keeweelol/Hikers-Companion/Lora Source/dimensions/README.md

# Shell

| Board | Shell |
| --- | --- |
| T-Beam-Supreme | [Shell](./T-Beam-Suppeme.7z) |
| T-Beam-V1.1/V1.2 | [Shell](./T-Beam-V1X.7z) |
| T3-V2.1-1.6 | [Shell](./T3-V2.1-1.6.7z) |
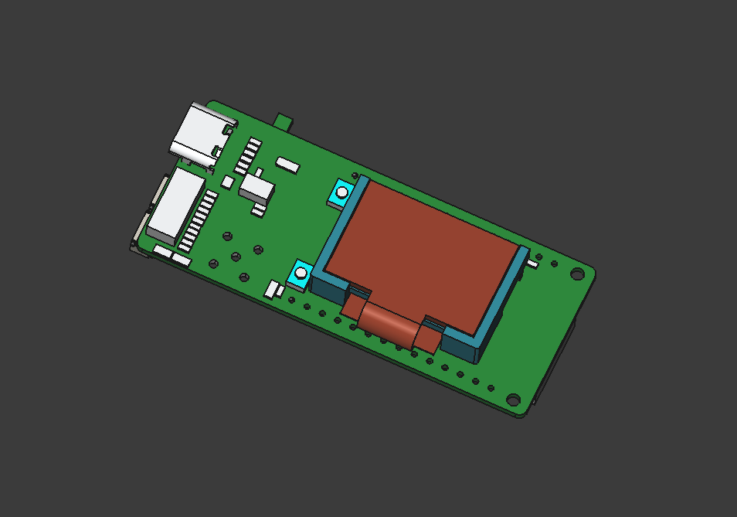
[picture p22: Lora Source/dimensions/images/T3S3-OLED.png]
| T3-S3 OLED |  |
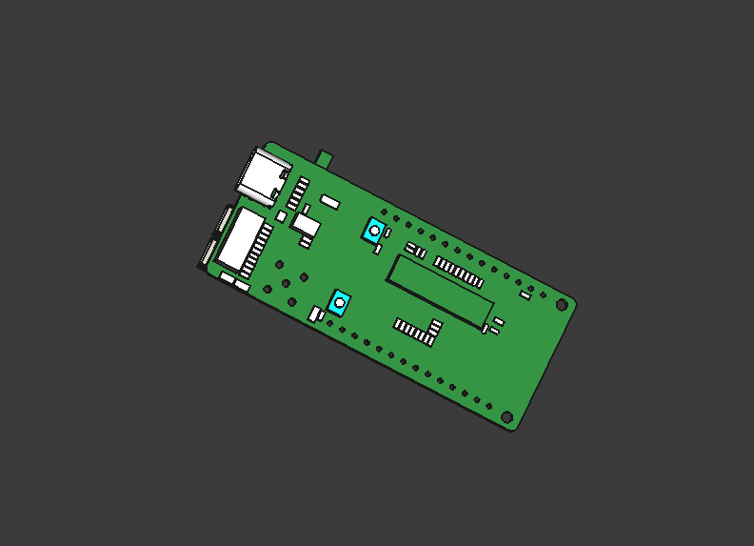
[picture p23: Lora Source/dimensions/images/T3S3.png]
| T3-S3 |  |
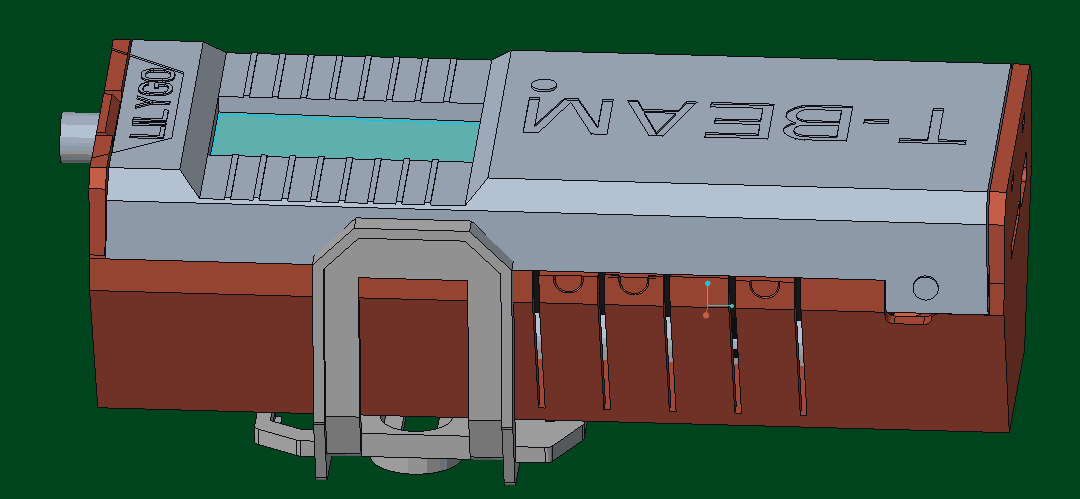
[picture p24: Lora Source/dimensions/images/T-Beam-Supreme-Shell.png]
Shell
| T-Beam-Supreme-Shell.7z |  |
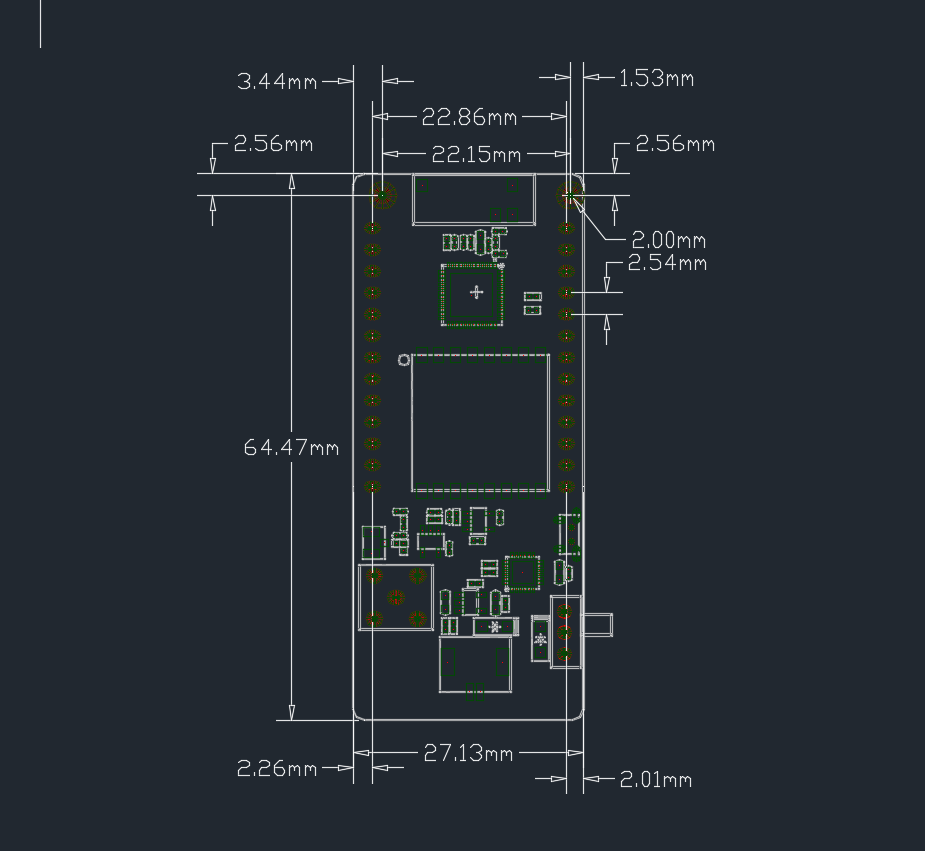
[picture p25: Lora Source/dimensions/images/T3-V1.6-DXF.png]
| T3-V1.6.2 |  |
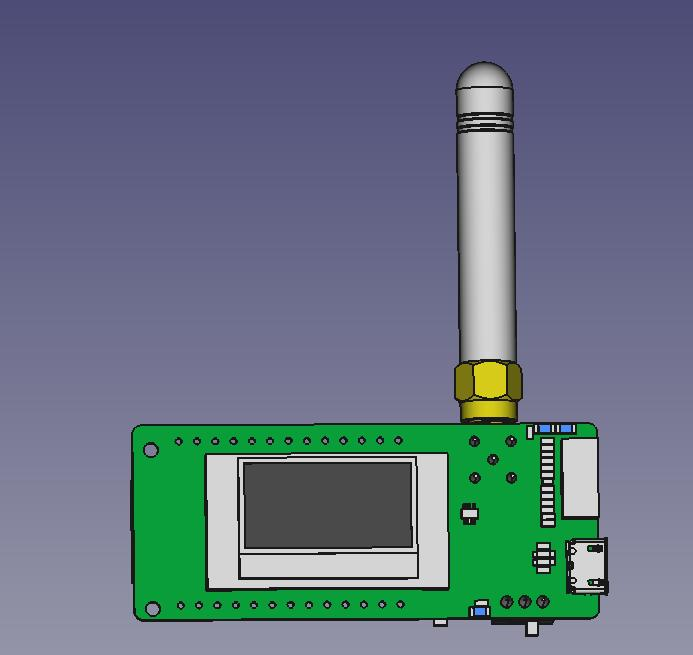
[picture p26: Lora Source/dimensions/images/T3-V1.6-PCB.jpg]
| T3_V1.6_PCB_3D.7z |  |
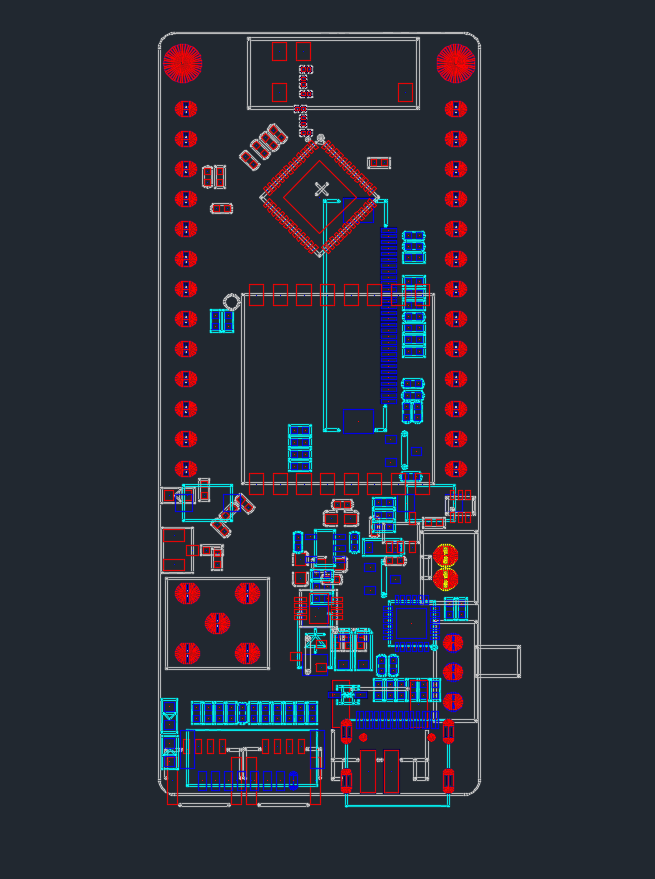
[picture p27: Lora Source/dimensions/images/T3 TCXO.png]
| TT3_V3.0_TCXO |  |
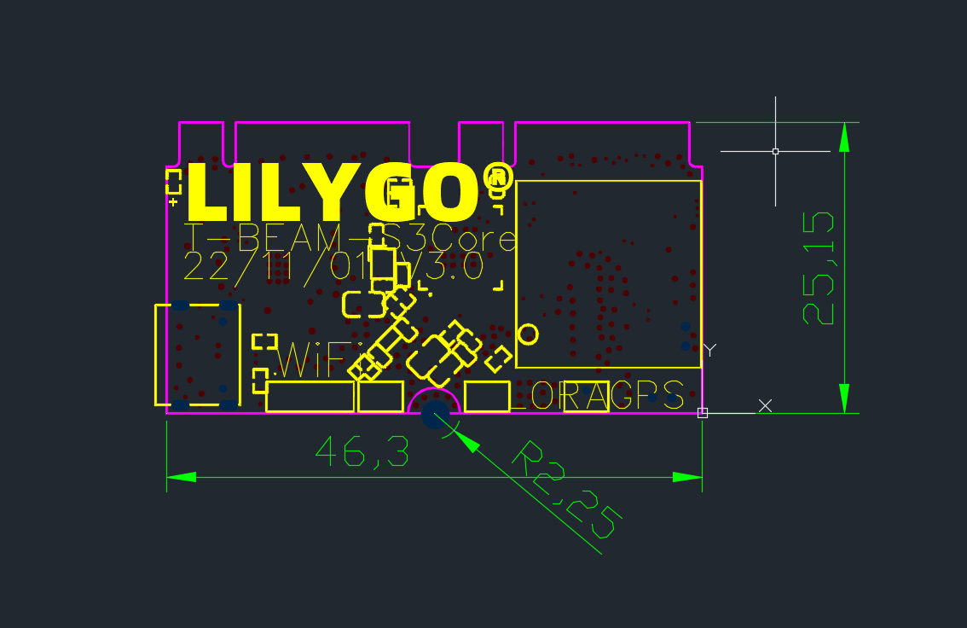
[picture p28: Lora Source/dimensions/images/T-Beam-S3.png]
| T-Beam-S3-Core |  |
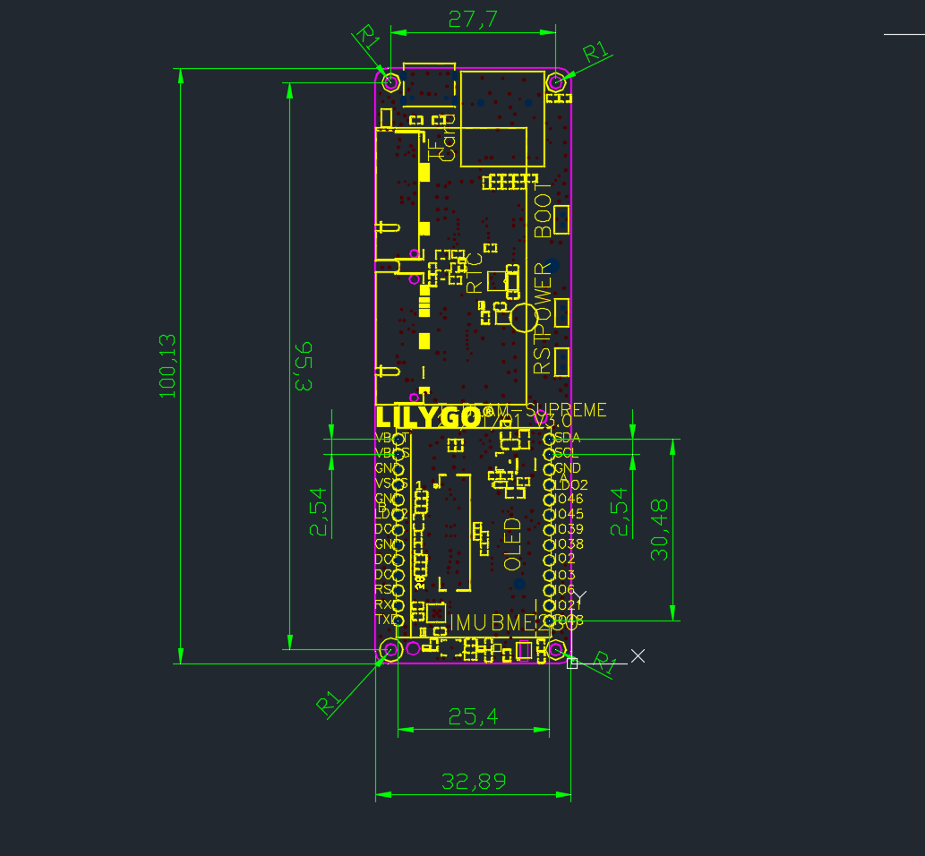
[picture p29: Lora Source/dimensions/images/T-Beam-Supreme.png]
| T-Beam-Supreme |  |
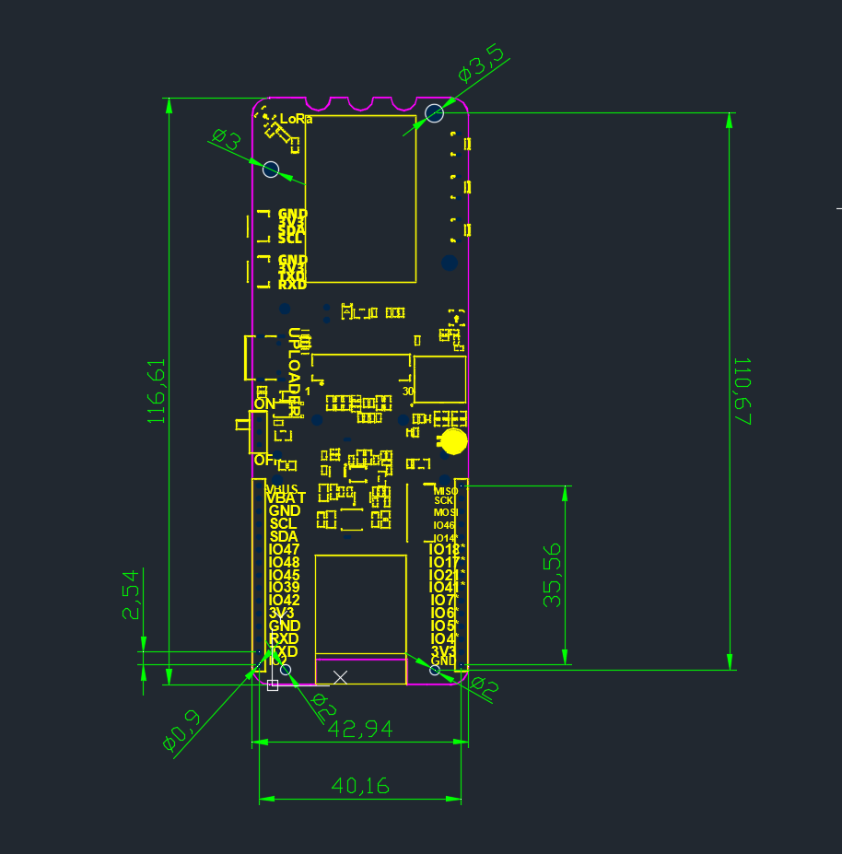
[picture p30: Lora Source/dimensions/images/t-beam-1w-dwg.png]
| T-Beam-1W |  |
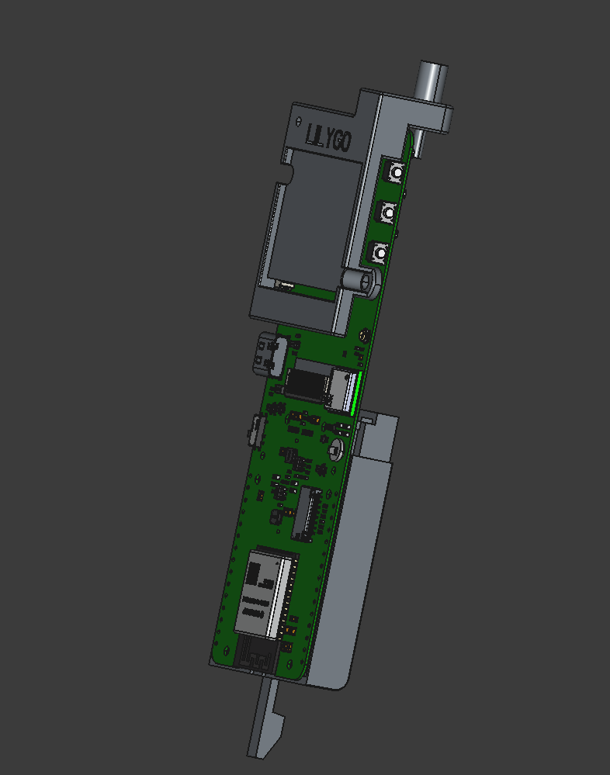
[picture p31: Lora Source/dimensions/images/t-beam-1w.png]
| T-Beam-1W |  |
