keeweelol/Hikers-Companion/Lora Source/assets/image/GPS_EN.jpg

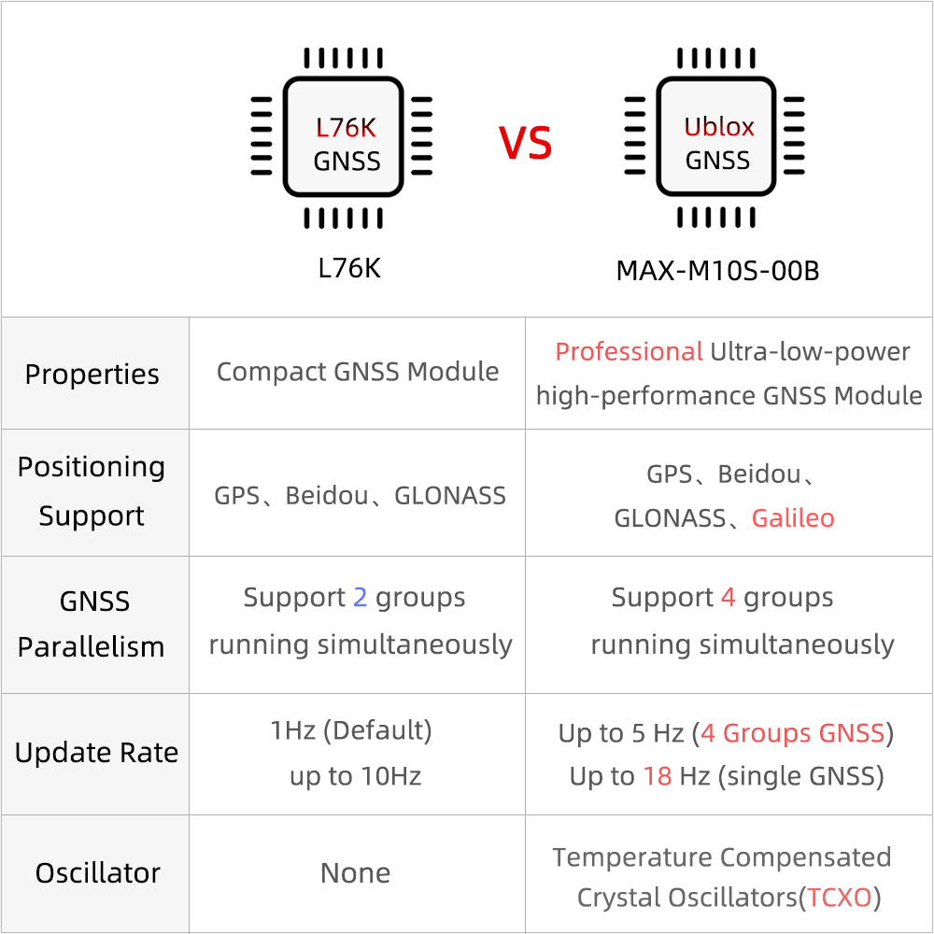
Lora Source/assets/image/GPS_EN.jpg
