keeweelol/Hikers-Companion/Lora Source/assets/image/lora32_v1.3_pinmap.jpg

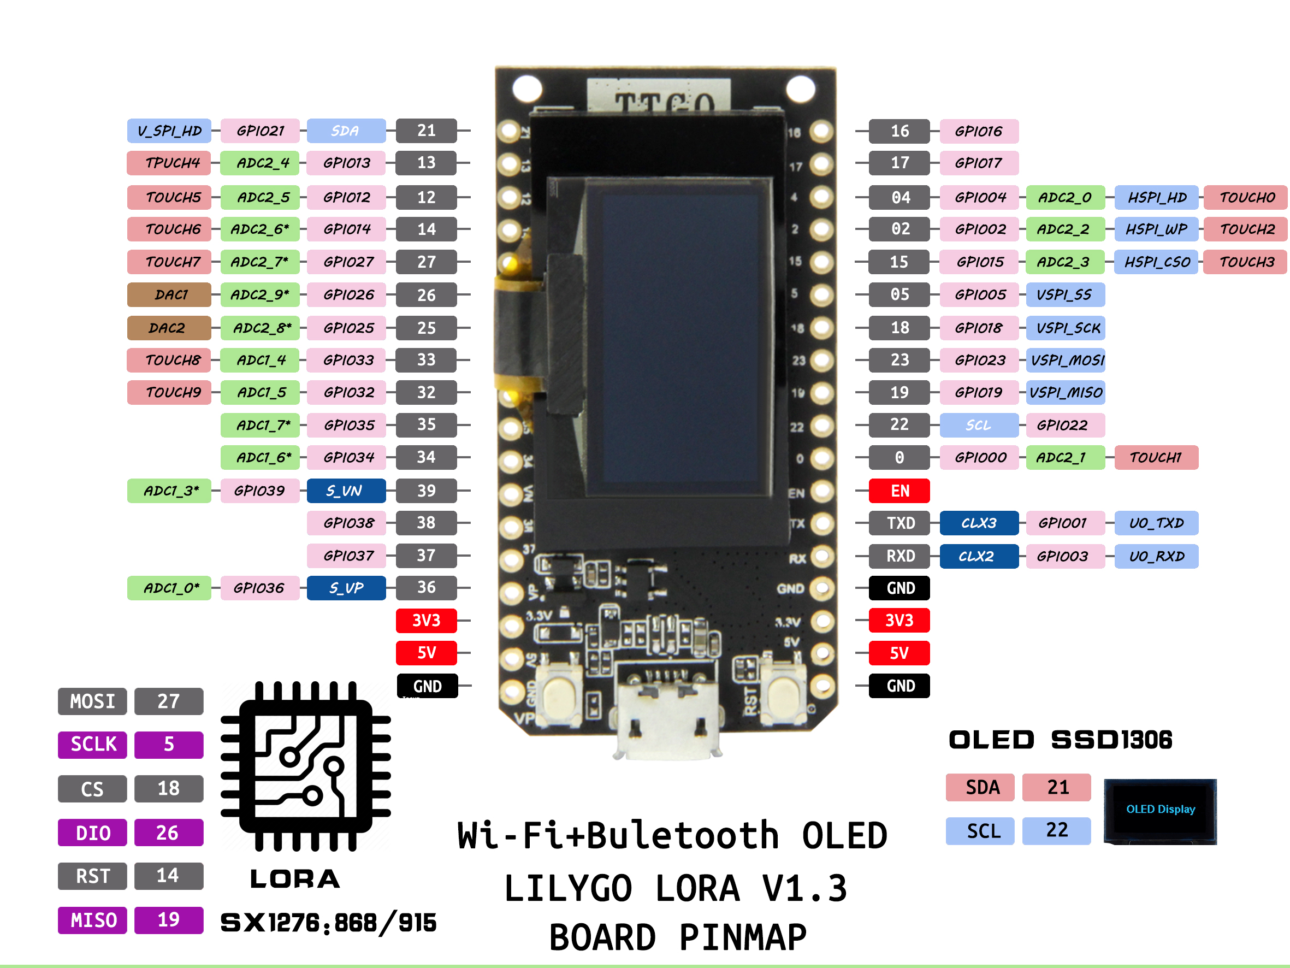
Lora Source/assets/image/lora32_v1.3_pinmap.jpg
