keeweelol/Hikers-Companion/Lora Source/assets/image/lora32_v1.8_pinmap.jpg

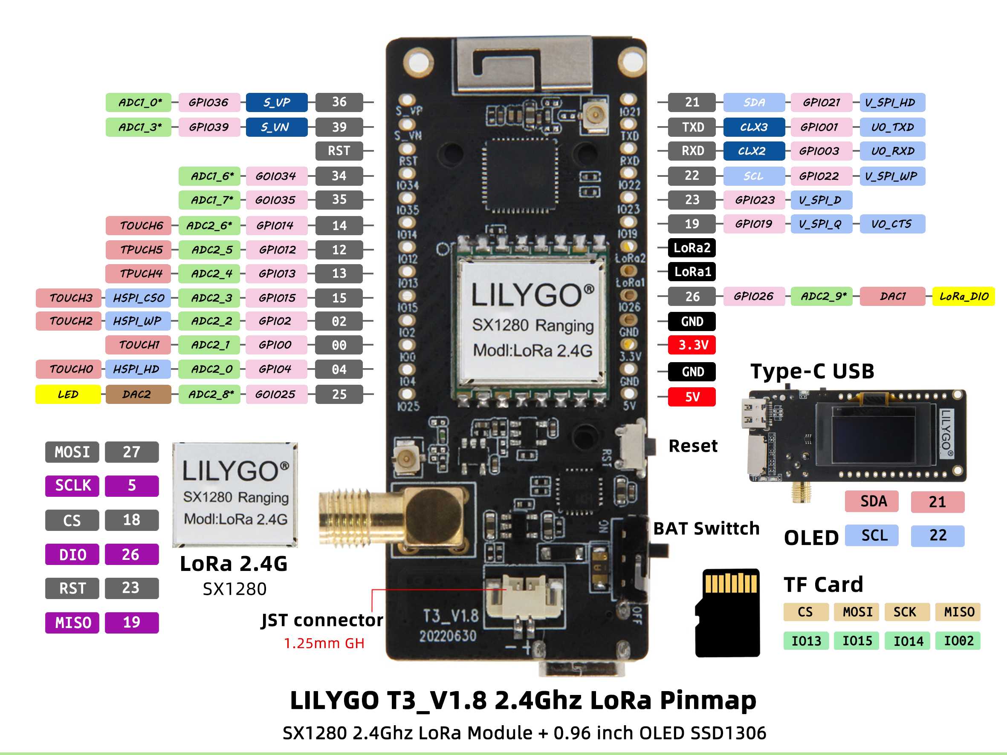
Lora Source/assets/image/lora32_v1.8_pinmap.jpg
