keeweelol/Hikers-Companion/Lora Source/assets/image/lora32_v2.0_pinmap.jpg

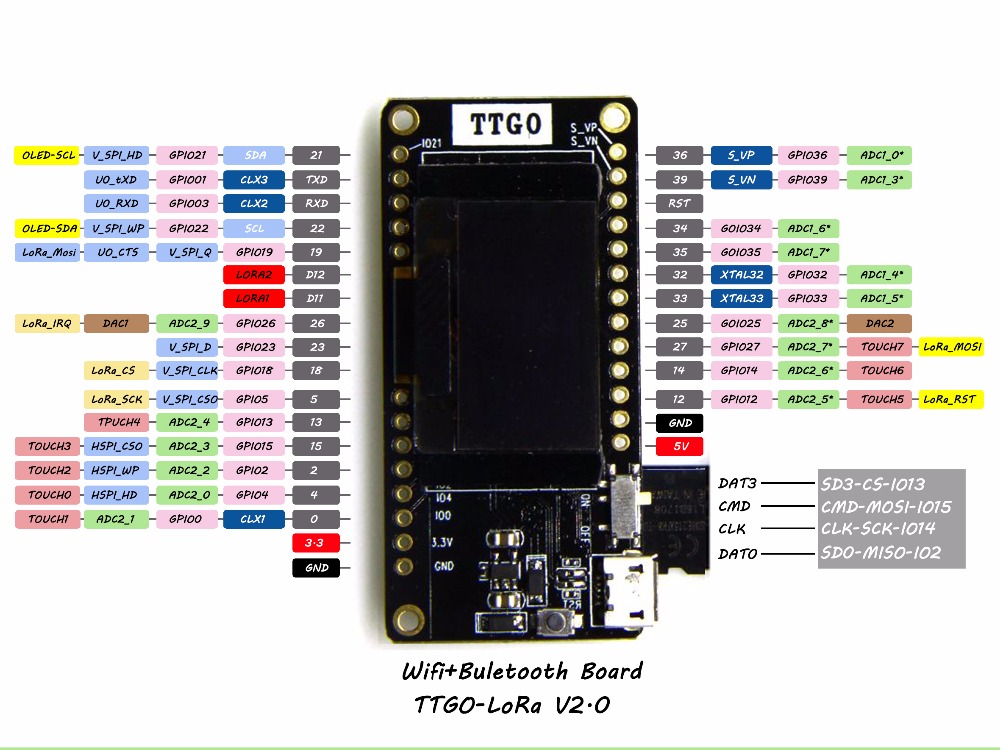
Lora Source/assets/image/lora32_v2.0_pinmap.jpg
