keeweelol/Hikers-Companion/Lora Source/assets/image/T-BEAM-S3-Supreme.jpg

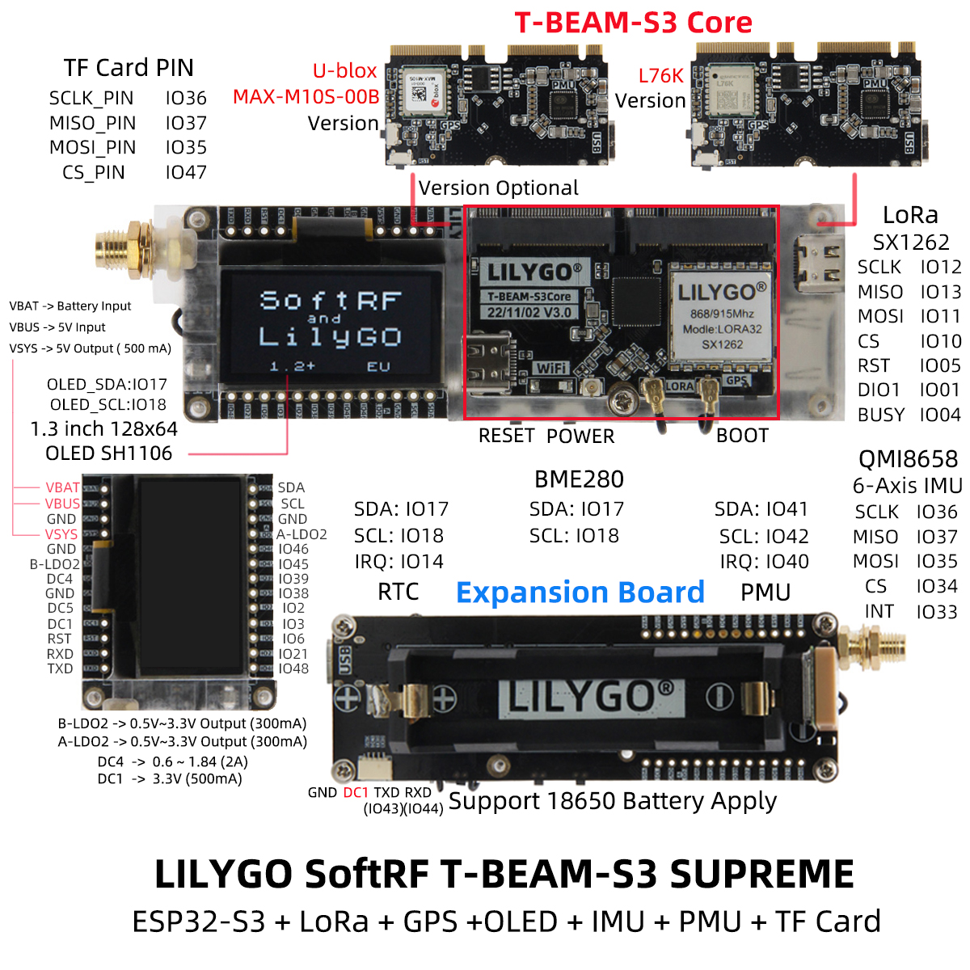
Lora Source/assets/image/T-BEAM-S3-Supreme.jpg
