keeweelol/Hikers-Companion/Lora Source/assets/image/t-beam_v1.1_pinmap.jpg

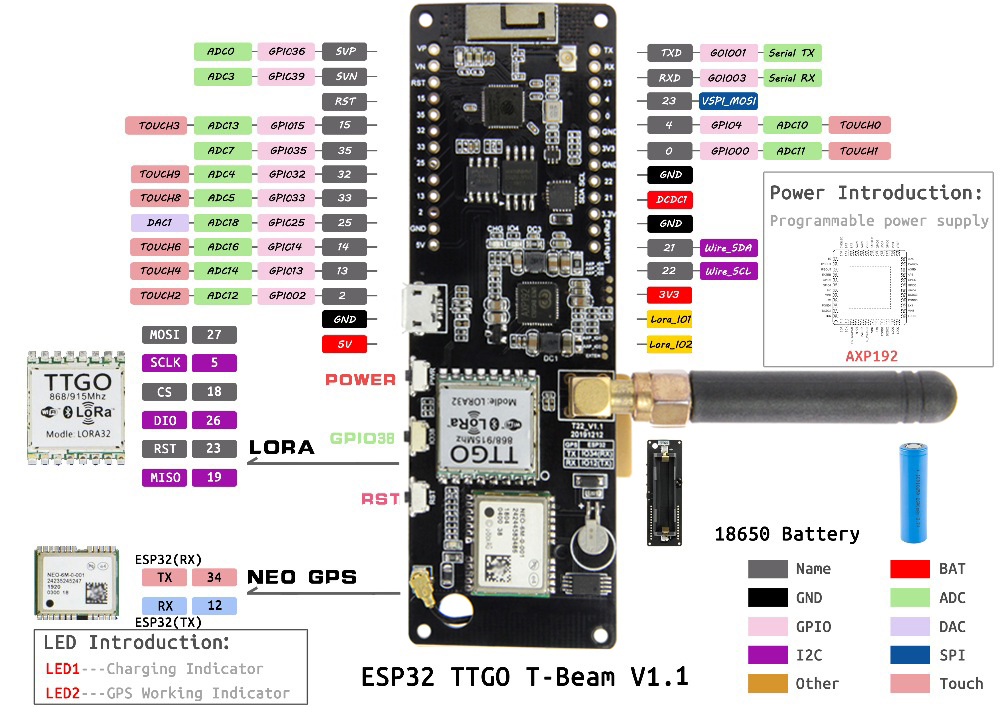
Lora Source/assets/image/t-beam_v1.1_pinmap.jpg
