keeweelol/Hikers-Companion/Lora Source/assets/image/t-motion_v1.0_pinmap.jpg

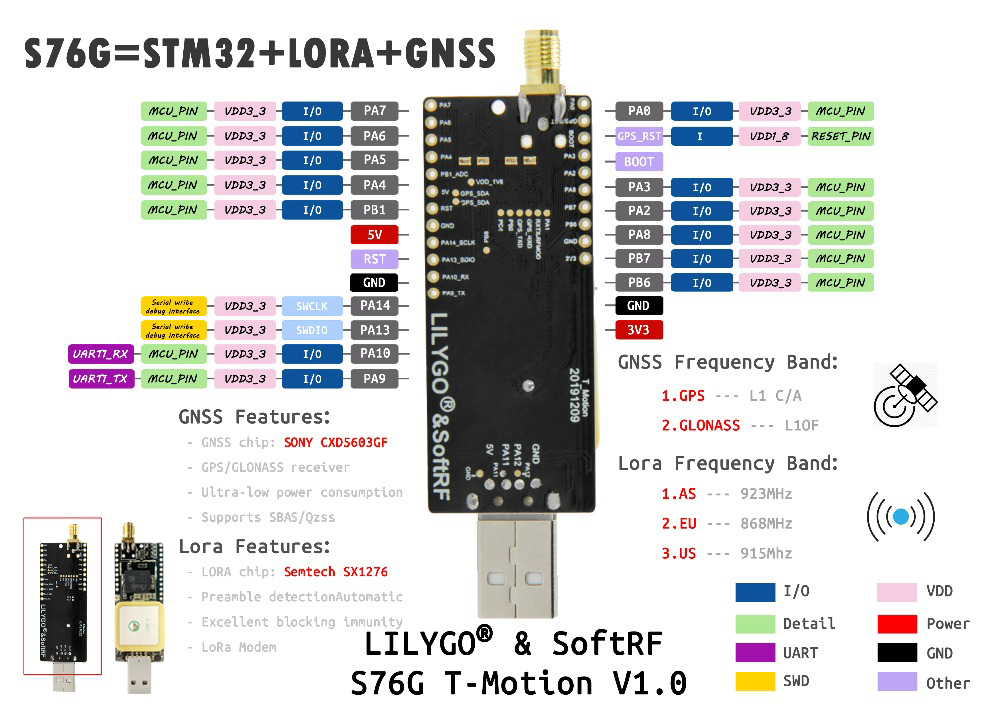
Lora Source/assets/image/t-motion_v1.0_pinmap.jpg
