keeweelol/Hikers-Companion/Lora Source/examples/T3S3Factory/images/T3_S3_V1.3_DeepSleepCurrent.jpg

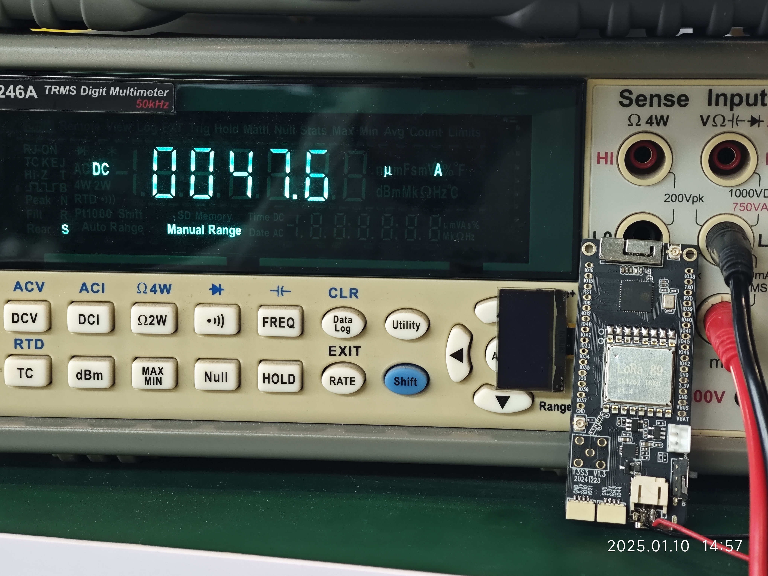
Lora Source/examples/T3S3Factory/images/T3_S3_V1.3_DeepSleepCurrent.jpg
