keeweelol/Hikers-Companion/Lora Source/examples/TBeamFactory/images/TIMER_WAKEUP_ADD_GPIO_WAKEUP_ext1_ext0_SLEEP_CUR.jpg

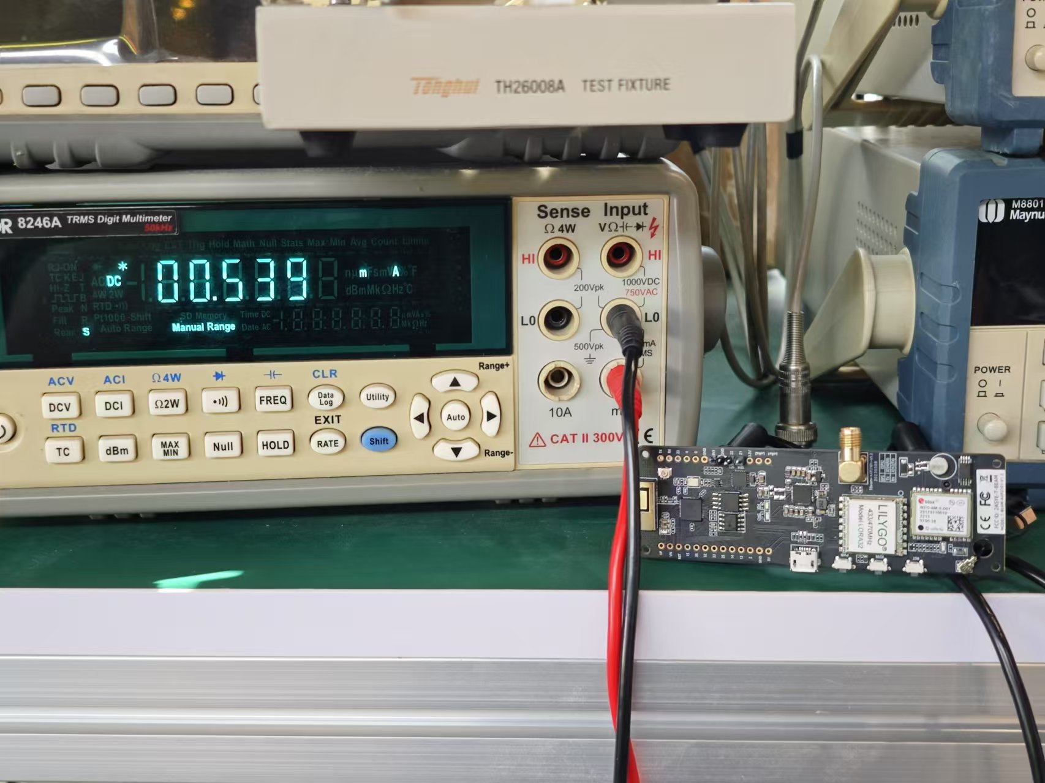
Lora Source/examples/TBeamFactory/images/TIMER_WAKEUP_ADD_GPIO_WAKEUP_ext1_ext0_SLEEP_CUR.jpg
