keeweelol/Hikers-Companion/Lora Source/examples/TBeamFactory/images/TIMER_WAKEUP_ADD_GPIO_WAKEUP_SLEEP_CUR_Disp.jpg

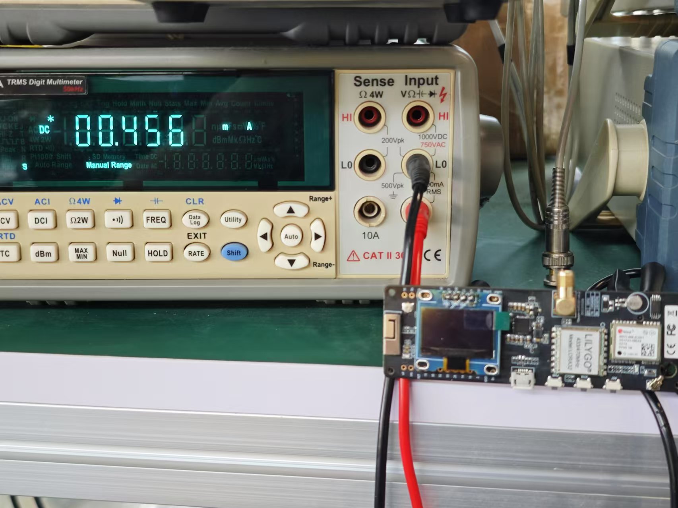
Lora Source/examples/TBeamFactory/images/TIMER_WAKEUP_ADD_GPIO_WAKEUP_SLEEP_CUR_Disp.jpg
