keeweelol/Hikers-Companion/Lora Source/firmware/images/u-center2.gif

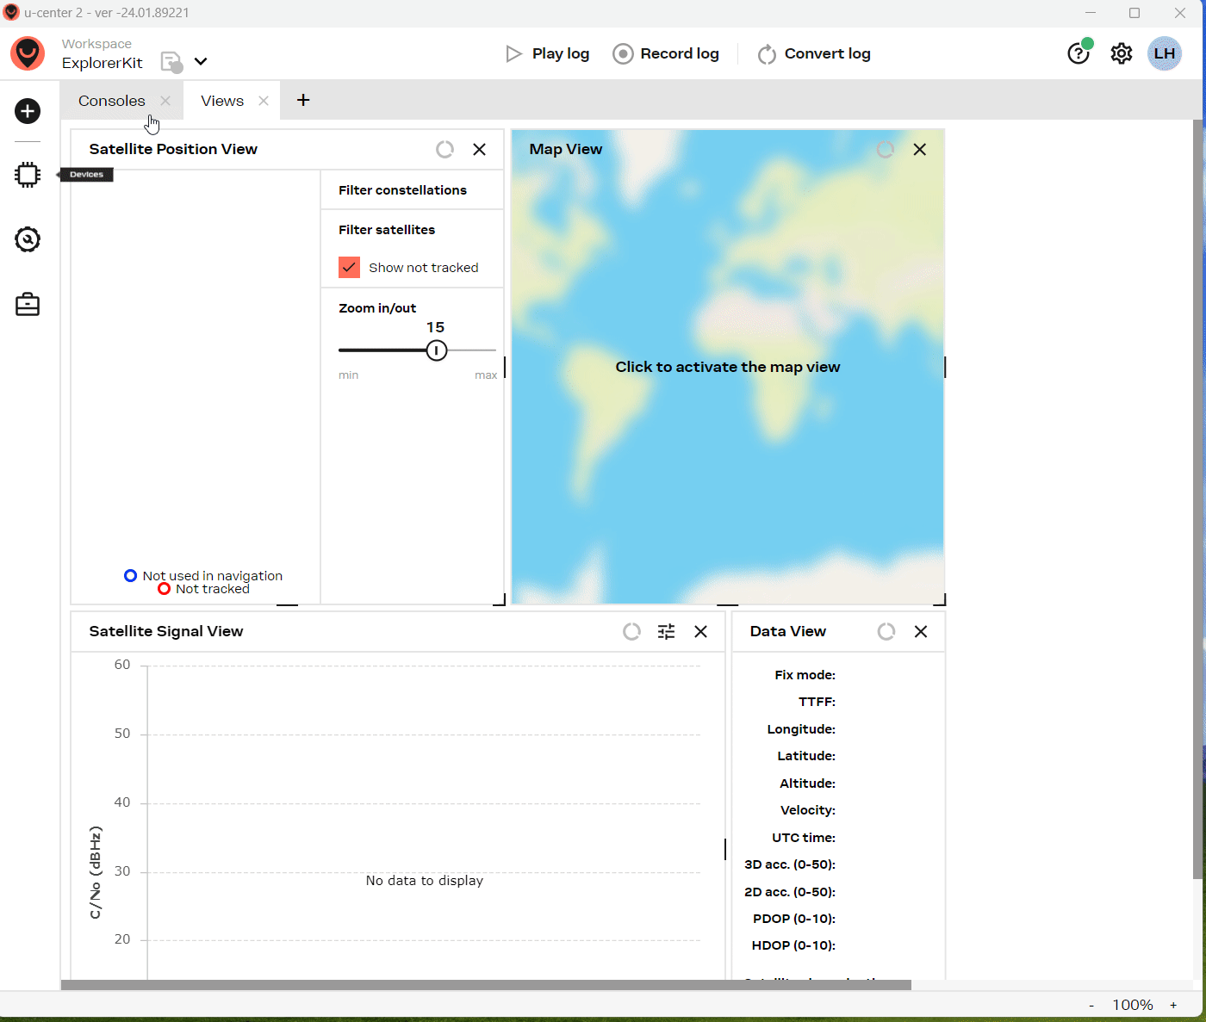
Lora Source/firmware/images/u-center2.gif
