keeweelol/Hikers-Companion/Lora Source/firmware/hardware_test/lT3_C6_V1.0_850/SETTING.jpg

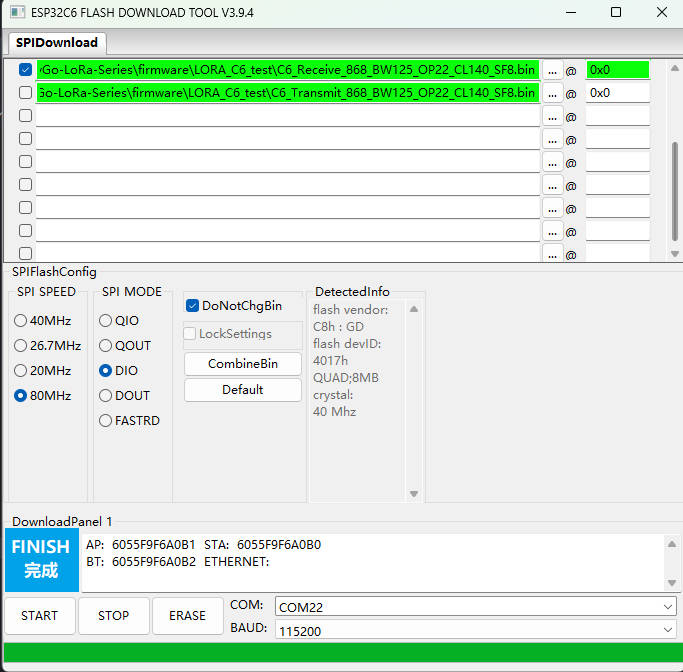
Lora Source/firmware/hardware_test/lT3_C6_V1.0_850/SETTING.jpg
