keeweelol/Hikers-Companion/Lora Source/examples/OLED/SH1106FontUsage/SH1106FontUsage.ino

/*

  FontUsage.ino

  How to overwrite previous text with a new text.
  How to avoid the buffer clear command.

  Universal 8bit Graphics Library (https://github.com/olikraus/disp/)

  Copyright (c) 2016, olikraus@gmail.com
  All rights reserved.

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
  THIS SOFTWARE IS PROVIDED BY THE COPYRIGHT HOLDERS AND
  CONTRIBUTORS "AS IS" AND ANY EXPRESS OR IMPLIED WARRANTIES,
  INCLUDING, BUT NOT LIMITED TO, THE IMPLIED WARRANTIES OF
  MERCHANTABILITY AND FITNESS FOR A PARTICULAR PURPOSE ARE
  DISCLAIMED. IN NO EVENT SHALL THE COPYRIGHT HOLDER OR
  CONTRIBUTORS BE LIABLE FOR ANY DIRECT, INDIRECT, INCIDENTAL,
  SPECIAL, EXEMPLARY, OR CONSEQUENTIAL DAMAGES (INCLUDING, BUT
  NOT LIMITED TO, PROCUREMENT OF SUBSTITUTE GOODS OR SERVICES;
  LOSS OF USE, DATA, OR PROFITS; OR BUSINESS INTERRUPTION) HOWEVER
  CAUSED AND ON ANY THEORY OF LIABILITY, WHETHER IN CONTRACT,
  STRICT LIABILITY, OR TORT (INCLUDING NEGLIGENCE OR OTHERWISE)
  ARISING IN ANY WAY OUT OF THE USE OF THIS SOFTWARE, EVEN IF
  ADVISED OF THE POSSIBILITY OF SUCH DAMAGE.


  Usually, a sequence like this is used:
  disp->clearBuffer();                   // clear the internal memory
  disp->setFont(u8g2_font_ncenB08_tr);   // choose a suitable font
  disp->setCursor(0,20)              // set write position
  disp->print("Hello World!");           // write something to the internal memory
  disp->sendBuffer();                    // transfer internal memory to the display

  In order to speed up the display content rendering for any modified text,
  we could drop the clearBuffer command and just overwrite the previous string:

  disp->setFont(u8g2_font_ncenB08_tr);   // choose a suitable font
  disp->setCursor(0,20)              // set write position
  disp->print("hello there");            // write something to the internal memory
  disp->sendBuffer();                    // transfer internal memory to the display

  This will only work if:
  - Background is drawn
  - All gylphs have the same height
  Additionally some extra spaces are required of the new text is shorter than the
  previous one.

  To draw the background: use font mode 0
  To ensure that all glyphs have the same height, use h or m fonts.

  disp->setFontMode(0);              // write solid glyphs
  disp->setFont(u8g2_font_ncenB08_hr);   // choose a suitable h font
  disp->setCursor(0,20)              // set write position
  disp->print("hello there  ");          // use extra spaces here
  disp->sendBuffer();                    // transfer internal memory to the display


*/

#include <Arduino.h>
#include "LoRaBoards.h"


#define INFO_SCREEN_DELAY 3000

/*
  Linear Congruential Generator (LCG)
  z = (a*z + c) % m;
  m = 256 (8 Bit)

  for period:
  a-1: dividable by 2
  a-1: multiple of 4
  c: not dividable by 2

  c = 17
  a-1 = 64 --> a = 65
*/
uint8_t z = 127;    // start value
uint32_t lcg_rnd(void)
{
    z = (uint8_t)((uint16_t)65 * (uint16_t)z + (uint16_t)17);
    return (uint32_t)z;
}

void setup(void)
{
    setupBoards();
    if (!disp) {
        Serial.println("No find SH1106 display!Please check whether the connection is normal");
        while (1);
    }
}

void draw(int is_blank)
{
    int i, j;
    int n;
    char s[4];

    for ( j = 0; j < 20; j++ ) {
        // random number
        n = lcg_rnd();

        // random string
        for ( i = 0; i < 3; i++ ) {
            s[i] = lcg_rnd() >> 3;
            if ( s[i] < 16 )
                s[i] += 'a';
            else
                s[i] += 'A';
        }
        s[3] = '\0';

        // print number
        disp->setCursor(0, 15);
        disp->print("Number: ");
        if ( is_blank )
            disp->print("       ");
        disp->setCursor(70, 15);
        disp->print(n);


        // print string
        disp->setCursor(0, 30);
        disp->print("Text: ");
        disp->setCursor(70, 30);
        disp->print(s);
        if ( is_blank )
            disp->print("        ");

        // make the result visible
        disp->sendBuffer();

        // delay, so that the user can see the result
        delay(200);
    }
}

void draw_m1_t()
{
    disp->clearBuffer();

    disp->setFontMode(1);
    disp->setFont(u8g2_font_cu12_tr);

    disp->setCursor(0, 15);
    disp->print(F("setFontMode(1);"));
    disp->setCursor(0, 30);
    disp->print(F("setFont(..._tr);"));
    disp->setCursor(0, 55);
    disp->print(F("Very Bad"));

    disp->sendBuffer();
    delay(INFO_SCREEN_DELAY);

    disp->setFontMode(1);
    disp->setFont(u8g2_font_cu12_tr);
    disp->clearBuffer();                   // clear the internal memory once
    draw(0);
}

void draw_m0_t()
{
    disp->clearBuffer();

    disp->setFontMode(1);
    disp->setFont(u8g2_font_cu12_tr);

    disp->setCursor(0, 15);
    disp->print(F("setFontMode(0);"));
    disp->setCursor(0, 30);
    disp->print(F("setFont(.._tr);"));
    disp->setCursor(0, 55);
    disp->print(F("Wrong"));

    disp->sendBuffer();
    delay(INFO_SCREEN_DELAY);

    disp->setFontMode(0);
    disp->setFont(u8g2_font_cu12_tr);
    disp->clearBuffer();                   // clear the internal memory once
    draw(0);
}

void draw_m1_h()
{
    disp->clearBuffer();

    disp->setFontMode(1);
    disp->setFont(u8g2_font_cu12_tr);

    disp->setCursor(0, 15);
    disp->print(F("setFontMode(0);"));
    disp->setCursor(0, 30);
    disp->print(F("setFont(.._hr);"));
    disp->setCursor(0, 55);
    disp->print(F("Still bad"));

    disp->sendBuffer();
    delay(INFO_SCREEN_DELAY);

    disp->setFontMode(1);
    disp->setFont(u8g2_font_cu12_hr);
    disp->clearBuffer();                   // clear the internal memory once
    draw(0);
}

void draw_m0_h()
{
    disp->clearBuffer();

    disp->setFontMode(1);
    disp->setFont(u8g2_font_cu12_tr);

    disp->setCursor(0, 15);
    disp->print(F("setFontMode(0);"));
    disp->setCursor(0, 30);
    disp->print(F("setFont(.._hr);"));
    disp->setCursor(0, 55);
    disp->print(F("Almost ok"));

    disp->sendBuffer();
    delay(INFO_SCREEN_DELAY);

    disp->setFontMode(0);
    disp->setFont(u8g2_font_cu12_hr);
    disp->clearBuffer();                   // clear the internal memory once
    draw(0);
}

void draw_m0_h_with_extra_blank()
{
    disp->clearBuffer();

    disp->setFontMode(1);
    disp->setFont(u8g2_font_cu12_tr);

    disp->setCursor(0, 15);
    disp->print(F("setFontMode(0);"));
    disp->setCursor(0, 30);
    disp->print(F("setFont(.._hr);"));
    disp->setCursor(0, 55);
    disp->print(F("Extra blank --> Ok"));

    disp->sendBuffer();
    delay(INFO_SCREEN_DELAY);

    disp->setFontMode(0);
    disp->setFont(u8g2_font_cu12_hr);
    disp->clearBuffer();                   // clear the internal memory once
    draw(1);
}


void loop(void)
{

    // This problem applies only to full buffer mode
    disp->clearBuffer();
    disp->setFontMode(1);
    disp->setFont(u8g2_font_cu12_tr);
    disp->setCursor(0, 15);
    disp->print(F("Problems with"));
    disp->setCursor(0, 30);
    disp->print(F("full buffer mode"));
    disp->setCursor(0, 45);
    disp->print(F("and skipped clear."));
    disp->sendBuffer();
    delay(INFO_SCREEN_DELAY);


    draw_m1_t();          // fontmode 1, t font --> wrong
    draw_m1_h();          // fontmode 1, h font --> wrong
    draw_m0_t();          // fontmode 0, t font --> wrong
    draw_m0_h();          // fontmode 1, h font --> ok
    draw_m0_h_with_extra_blank(); // fontmode 1, h font with extra blank --> correct
    delay(1000);
}
