keeweelol/Hikers-Companion/Lora Source/examples/OLED/SH1106IconMenu/SH1106IconMenu.ino

/*

  IconMenu.ino

  This is an interactive demo and requires "next", "prev" and "select" button.
  Minimum height of the display should be 64.

  Universal 8bit Graphics Library (https://github.com/olikraus/disp/)

  Copyright (c) 2016, olikraus@gmail.com
  All rights reserved.

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
  THIS SOFTWARE IS PROVIDED BY THE COPYRIGHT HOLDERS AND
  CONTRIBUTORS "AS IS" AND ANY EXPRESS OR IMPLIED WARRANTIES,
  INCLUDING, BUT NOT LIMITED TO, THE IMPLIED WARRANTIES OF
  MERCHANTABILITY AND FITNESS FOR A PARTICULAR PURPOSE ARE
  DISCLAIMED. IN NO EVENT SHALL THE COPYRIGHT HOLDER OR
  CONTRIBUTORS BE LIABLE FOR ANY DIRECT, INDIRECT, INCIDENTAL,
  SPECIAL, EXEMPLARY, OR CONSEQUENTIAL DAMAGES (INCLUDING, BUT
  NOT LIMITED TO, PROCUREMENT OF SUBSTITUTE GOODS OR SERVICES;
  LOSS OF USE, DATA, OR PROFITS; OR BUSINESS INTERRUPTION) HOWEVER
  CAUSED AND ON ANY THEORY OF LIABILITY, WHETHER IN CONTRACT,
  STRICT LIABILITY, OR TORT (INCLUDING NEGLIGENCE OR OTHERWISE)
  ARISING IN ANY WAY OUT OF THE USE OF THIS SOFTWARE, EVEN IF
  ADVISED OF THE POSSIBILITY OF SUCH DAMAGE.

*/

#include <Arduino.h>
#include "LoRaBoards.h"

void setup(void)
{
    setupBoards();
    if (!disp) {
        Serial.println("No find SH1106 display!Please check whether the connection is normal");
        while (1);
    }
    disp->setFont(u8g2_font_6x12_tr);
}

struct menu_entry_type {
    const uint8_t *font;
    uint16_t icon;
    const char *name;
};

struct menu_state {
    int16_t menu_start;       /* in pixel */
    int16_t frame_position;       /* in pixel */
    uint8_t position;         /* position, array index */
};

/*
  Icon configuration
  Width and height must match the icon font size
  GAP: Space between the icons
  BGAP: Gap between the display border and the cursor.
*/
#define ICON_WIDTH 32
#define ICON_HEIGHT 32
#define ICON_GAP 4
#define ICON_BGAP 16
#define ICON_Y 32+ ICON_GAP

struct menu_entry_type menu_entry_list[] = {
    { u8g2_font_open_iconic_embedded_4x_t, 65, "Clock Setup"},
    { u8g2_font_open_iconic_embedded_4x_t, 66, "Gear Game"},
    { u8g2_font_open_iconic_embedded_4x_t, 67, "Flash Light"},
    { u8g2_font_open_iconic_embedded_4x_t, 68, "Home"},
    { u8g2_font_open_iconic_embedded_4x_t, 72, "Configuration"},
    { NULL, 0, NULL }
};

void draw(struct menu_state *state)
{
    int16_t x;
    uint8_t i;
    x = state->menu_start;
    i = 0;
    while ( menu_entry_list[i].icon > 0 ) {
        if ( x >= -ICON_WIDTH && x < disp->getDisplayWidth() ) {
            disp->setFont(menu_entry_list[i].font);
            disp->drawGlyph(x, ICON_Y, menu_entry_list[i].icon );
        }
        i++;
        x += ICON_WIDTH + ICON_GAP;
    }
    disp->drawFrame(state->frame_position - 1, ICON_Y - ICON_HEIGHT - 1, ICON_WIDTH + 2, ICON_WIDTH + 2);
    disp->drawFrame(state->frame_position - 2, ICON_Y - ICON_HEIGHT - 2, ICON_WIDTH + 4, ICON_WIDTH + 4);
    disp->drawFrame(state->frame_position - 3, ICON_Y - ICON_HEIGHT - 3, ICON_WIDTH + 6, ICON_WIDTH + 6);
}


void to_right(struct menu_state *state)
{
    if ( menu_entry_list[state->position + 1].font != NULL ) {
        if ( (int16_t)state->frame_position + 2 * (int16_t)ICON_WIDTH + (int16_t)ICON_BGAP < (int16_t)disp->getDisplayWidth() ) {
            state->position++;
            state->frame_position += ICON_WIDTH + (int16_t)ICON_GAP;
        } else {
            state->position++;
            state->frame_position = (int16_t)disp->getDisplayWidth() - (int16_t)ICON_WIDTH - (int16_t)ICON_BGAP;
            state->menu_start = state->frame_position - state->position * ((int16_t)ICON_WIDTH + (int16_t)ICON_GAP);
        }
    }
}

void to_left(struct menu_state *state)
{
    if ( state->position > 0 ) {
        if ( (int16_t)state->frame_position >= (int16_t)ICON_BGAP + (int16_t)ICON_WIDTH + (int16_t)ICON_GAP ) {
            state->position--;
            state->frame_position -= ICON_WIDTH + (int16_t)ICON_GAP;
        } else {
            state->position--;
            state->frame_position = ICON_BGAP;
            state->menu_start = state->frame_position - state->position * ((int16_t)ICON_WIDTH + (int16_t)ICON_GAP);

        }
    }
}


uint8_t towards_int16(int16_t *current, int16_t dest)
{
    if ( *current < dest ) {
        (*current)++;
        return 1;
    } else if ( *current > dest ) {
        (*current)--;
        return 1;
    }
    return 0;
}

uint8_t towards(struct menu_state *current, struct menu_state *destination)
{
    uint8_t r = 0;
    r |= towards_int16( &(current->frame_position), destination->frame_position);
    r |= towards_int16( &(current->frame_position), destination->frame_position);
    r |= towards_int16( &(current->menu_start), destination->menu_start);
    r |= towards_int16( &(current->menu_start), destination->menu_start);
    return r;
}



struct menu_state current_state = { ICON_BGAP, ICON_BGAP, 0 };
struct menu_state destination_state = { ICON_BGAP, ICON_BGAP, 0 };

void loop(void)
{
    int8_t event;

    do {
        disp->clearBuffer();
        draw(&current_state);
        disp->setFont(u8g2_font_helvB10_tr);
        disp->setCursor((disp->getDisplayWidth() - disp->getStrWidth(menu_entry_list[destination_state.position].name)) / 2, disp->getDisplayHeight() - 5);
        disp->print(menu_entry_list[destination_state.position].name);
        disp->sendBuffer();
        delay(10);
        event = disp->getMenuEvent();
        if ( event == U8X8_MSG_GPIO_MENU_NEXT )
            to_right(&destination_state);
        if ( event == U8X8_MSG_GPIO_MENU_PREV )
            to_left(&destination_state);
        if ( event == U8X8_MSG_GPIO_MENU_SELECT ) {
            disp->setFont(u8g2_font_helvB10_tr);
            disp->userInterfaceMessage("Selection:", menu_entry_list[destination_state.position].name, "", " Ok ");
        }
    } while ( towards(&current_state, &destination_state) );
}
