keeweelol/Hikers-Companion/Lora Source/examples/Sensor/QMC63xx_GetDataExample/QMC63xx_GetDataExample.ino

/**
 *
 * @license MIT License
 *
 * Copyright (c) 2026 lewis he
 *
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
 * @file      QMC63xx_GetDataExample.ino
 * @author    Lewis He (lewishe@outlook.com)
 * @date      2026-04-08
 *
 */
#include <SensorQMC6310.hpp>
#include <SensorQMC6309.hpp>
#include <SensorWireHelper.h>
#include "LoRaBoards.h"

MagnetometerBase *magnetometer;

void setup()
{
    Serial.begin(115200);
    while (!Serial);

    setupBoards();

    // The desired output data rate in Hz.  Allowed values are 1.0, 10.0, 50.0, 100.0 and 200.0HZ.
    float data_rate_hz = 200.0f;
    // op_mode: Allowed values are SUSPEND, NORMAL, SINGLE_MEASUREMENT, CONTINUOUS_MEASUREMENT
    OperationMode op_mode = OperationMode::CONTINUOUS_MEASUREMENT;
    // full_scale: Allowed values are  FS_8G, FS_16G ,FS_32G
    MagFullScaleRange full_scale = MagFullScaleRange::FS_8G;
    // over_sample_ratio: Allowed values are OSR_1, OSR_2, OSR_4, OSR_8
    MagOverSampleRatio over_sample_ratio = MagOverSampleRatio::OSR_1;
    // down_sample_ratio: QMC6309 does not support downsampling rate settings; this parameter is ignored.
    MagDownSampleRatio down_sample_ratio = MagDownSampleRatio::DSR_1;



    SensorWireHelper::dumpDevices(Wire);

    if (magnetometer == nullptr) {
        magnetometer = new SensorQMC6310();
        if (!static_cast<SensorQMC6310*>(magnetometer)->begin(Wire, QMC6310U_SLAVE_ADDRESS, I2C_SDA, I2C_SCL)) {
            Serial.println("Failed to find QMC6310U - check your wiring!");
            delete magnetometer;
            magnetometer = nullptr;
        } else {
            Serial.println("QMC6310U found!");
            // The desired output data rate in Hz.  Allowed values are 10.0, 50.0, 100.0 and 200.0HZ.
            data_rate_hz = 200.0f;
            // op_mode: Allowed values are SUSPEND, NORMAL, SINGLE_MEASUREMENT, CONTINUOUS_MEASUREMENT
            op_mode = OperationMode::CONTINUOUS_MEASUREMENT;
            // full_scale: Allowed values are FS_2G, FS_8G, FS_12G ,FS_30G
            full_scale = MagFullScaleRange::FS_8G;
            // over_sample_ratio: Allowed values are OSR_1, OSR_2, OSR_4, OSR_8
            over_sample_ratio = MagOverSampleRatio::OSR_1;
            // down_sample_ratio: Allowed values are DSR_1, DSR_2, DSR_4, DSR_8
            down_sample_ratio = MagDownSampleRatio::DSR_1;
        }
    }

    if (magnetometer == nullptr) {
        magnetometer = new SensorQMC6310();
        if (!static_cast<SensorQMC6310*>(magnetometer)->begin(Wire, QMC6310N_SLAVE_ADDRESS, I2C_SDA, I2C_SCL)) {
            Serial.println("Failed to find QMC6310 - check your wiring!");
            delete magnetometer;
            magnetometer = nullptr;
        } else {
            Serial.println("QMC6310N found!");
            // The desired output data rate in Hz.  Allowed values are 10.0, 50.0, 100.0 and 200.0HZ.
            data_rate_hz = 200.0f;
            // op_mode: Allowed values are SUSPEND, NORMAL, SINGLE_MEASUREMENT, CONTINUOUS_MEASUREMENT
            op_mode = OperationMode::CONTINUOUS_MEASUREMENT;
            // full_scale: Allowed values are FS_2G, FS_8G, FS_12G ,FS_30G
            full_scale = MagFullScaleRange::FS_8G;
            // over_sample_ratio: Allowed values are OSR_1, OSR_2, OSR_4, OSR_8
            over_sample_ratio = MagOverSampleRatio::OSR_1;
            // down_sample_ratio: Allowed values are DSR_1, DSR_2, DSR_4, DSR_8
            down_sample_ratio = MagDownSampleRatio::DSR_1;
        }
    }

    if (magnetometer == nullptr) {
        magnetometer = new SensorQMC6309();
        if (!static_cast<SensorQMC6309*>(magnetometer)->begin(Wire, QMC6309_SLAVE_ADDRESS, I2C_SDA, I2C_SCL)) {
            Serial.println("Failed to find QMC6309 - check your wiring!");
            delete magnetometer;
            magnetometer = nullptr;
        } else {
            Serial.println("QMC6309 found!");
            // The desired output data rate in Hz.  Allowed values are 1.0, 10.0, 50.0, 100.0 and 200.0HZ.
            data_rate_hz = 200.0f;
            // op_mode: Allowed values are SUSPEND, NORMAL, SINGLE_MEASUREMENT, CONTINUOUS_MEASUREMENT
            op_mode = OperationMode::CONTINUOUS_MEASUREMENT;
            // full_scale: Allowed values are  FS_8G, FS_16G ,FS_32G
            full_scale = MagFullScaleRange::FS_8G;
            // over_sample_ratio: Allowed values are OSR_1, OSR_2, OSR_4, OSR_8
            over_sample_ratio = MagOverSampleRatio::OSR_1;
            // down_sample_ratio: QMC6309 does not support downsampling rate settings; this parameter is ignored.
            down_sample_ratio = MagDownSampleRatio::DSR_1;
        }
    }

    while (magnetometer == nullptr) {
        Serial.println("No magnetometer found!");
        delay(1000);
    }

    /* Config Magnetometer */
    if (magnetometer->configMagnetometer(
                op_mode,
                full_scale,
                data_rate_hz,
                over_sample_ratio,
                down_sample_ratio)) {
        Serial.println("Magnetometer configured successfully.");
    } else {
        Serial.println("Magnetometer configuration failed.");
        while (1);
    }

    SensorInfo info = magnetometer->getSensorInfo();
    Serial.print("Manufacturer: "); Serial.println(info.manufacturer);
    Serial.print("Model: "); Serial.println(info.model);
    Serial.print("I2C Address: 0x"); Serial.println(info.i2c_address, HEX);
    Serial.print("Version: "); Serial.println(info.version);
    Serial.print("UID: 0x"); Serial.println(info.uid);
    Serial.print("Type: "); Serial.println(SensorUtils::typeToString(info.type));

    SensorConfig cfg = magnetometer->getConfig();
    Serial.print("DataRate: "); Serial.println(cfg.sample_rate);
    Serial.print("FullScaleRange: "); Serial.println(cfg.range);
    Serial.print("Mode: "); Serial.println((uint8_t)cfg.mode);
    Serial.println();

    //Find the magnetic declination : https://www.magnetic-declination.com/
    float declination_deg = MagnetometerUtils::dmsToDecimalDegrees(-3, 20);   // -3.3333

    magnetometer->setDeclination(declination_deg);

    Serial.print(" Magnetic Declination: ");
    Serial.print(declination_deg, 2);
    Serial.println("°");

    Serial.print(" Sensitivity: ");
    Serial.print(magnetometer->getSensitivity(), 6);
    Serial.println(" Gauss/LSB");

    delay(3000);

    Serial.println("Read data now...");
}

void loop()
{

    MagnetometerData data;

    if (magnetometer->readData(data)) {

        // Gauss to μT
        float x = MagnetometerUtils::gaussToMicroTesla(data.magnetic_field.x);
        float y = MagnetometerUtils::gaussToMicroTesla(data.magnetic_field.y);
        float z = MagnetometerUtils::gaussToMicroTesla(data.magnetic_field.z);

        Serial.print("Mag:");
        Serial.print(" X:"); Serial.print(x);
        Serial.print(" Y:"); Serial.print(y);
        Serial.print(" Z:"); Serial.print(z);
        Serial.print(" μT");

        Serial.print(" Metadata:");
        Serial.print(" X:");
        Serial.print(data.raw.x);
        Serial.print(" Y:");
        Serial.print(data.raw.y);
        Serial.print(" Z:");
        Serial.print(data.raw.z);

        Serial.print(" Heading (rad): ");
        Serial.print(data.heading, 6);
        Serial.print(" rad");

        Serial.print(" Heading (deg): ");
        Serial.print(data.heading_degrees, 2);
        Serial.print("°");

        float strength = MagnetometerUtils::calculateMagneticStrength(data);
        Serial.print(" Magnetic Strength: ");
        Serial.print(strength, 2);
        Serial.println(" μT");

        if (data.overflow) {
            Serial.println("\tWarning: Data Overflow occurred!");
        }
    }
    delay(10);
}
